jeevanpillaystudio/vedya/src/public/f360-milestone-2/tile-magnet-fillet-2mm.stl

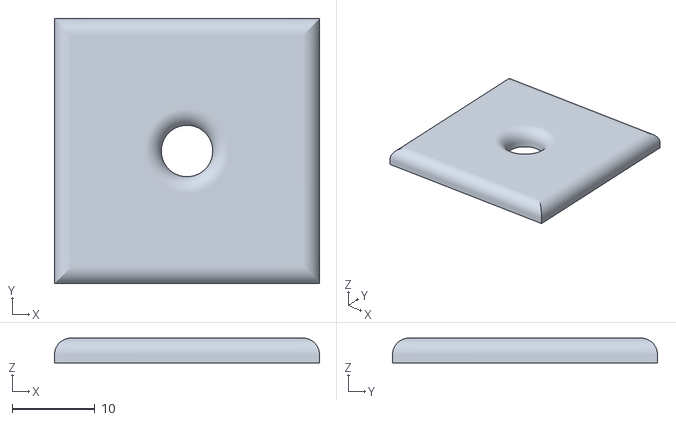
[picture p14: CAD file, 2024-09-06]
src/public/f360-milestone-2/tile-magnet-fillet-2mm.stl
32.0 x 32.0 x 3.00
