jeevanpillaystudio/vedya/src/public/f360-milestone-5/magnet-base-ring-thickness-0.20mm.stl

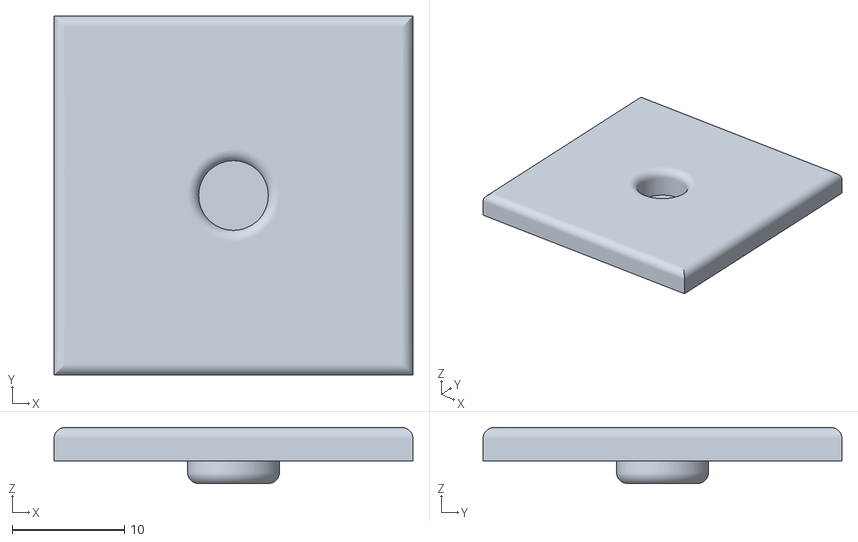
[picture p15: CAD file, 2024-09-06]
src/public/f360-milestone-5/magnet-base-ring-thickness-0.20mm.stl
32.0 x 32.0 x 5.00
