jeevanpillaystudio/vedya/src/public/f360-milestone-5/magnet-base-ring-thickness-0.25mm.stl

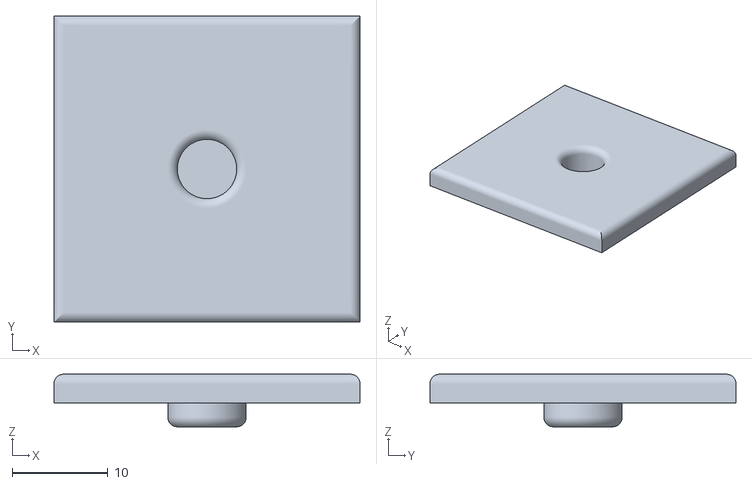
[picture p16: CAD file, 2024-09-06]
src/public/f360-milestone-5/magnet-base-ring-thickness-0.25mm.stl
32.0 x 32.0 x 5.50
